TenTelescopes/Skyward200/STL Files (alpha status not oriented)/D200 Astrograph Scope STLs/200mm Astrograph Dovetail.stl

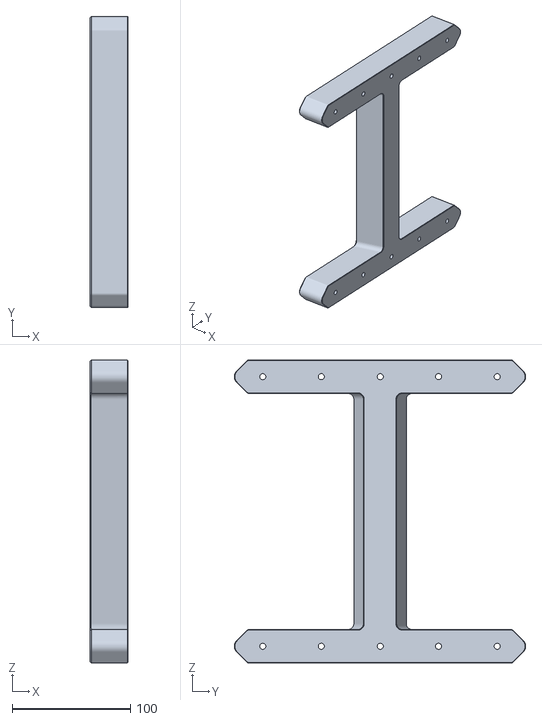
[picture p15: CAD file, 2026-08-10]
STL Files (alpha status not oriented)/D200 Astrograph Scope STLs/200mm Astrograph Dovetail.stl
32.0 x 246.8 x 256.6
