TenTelescopes/Skyward200/STL Files (alpha status not oriented)/D200 Visual Scope STLs/Accessories Printed Parts/Solar Finder Part 2.stl

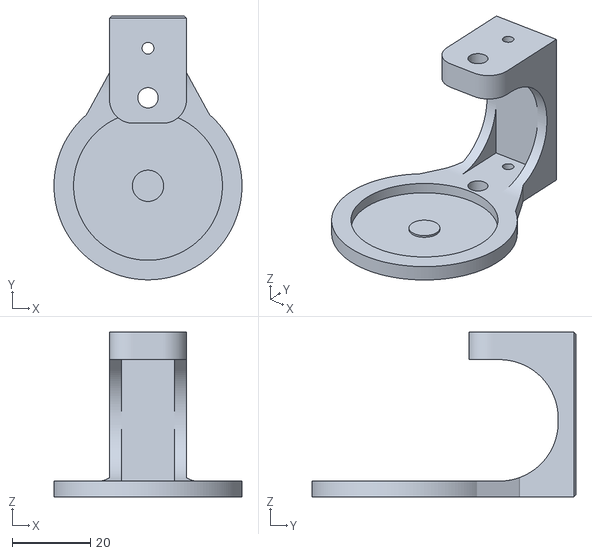
[picture p16: CAD file, 2026-08-24]
STL Files (alpha status not oriented)/D200 Visual Scope STLs/Accessories Printed Parts/Solar Finder Part 2.stl
48.0 x 67.3 x 42.0
