TenTelescopes/Skyward200/STL Files (alpha status not oriented)/D200 Visual Scope STLs/OTA Printed Parts/200mm Mirror Cell Cap.stl

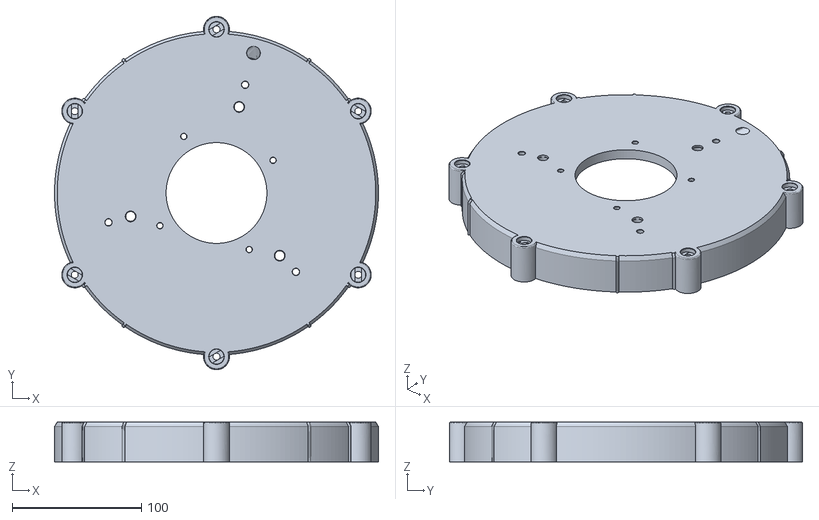
[picture p17: CAD file, 2026-05-24]
STL Files (alpha status not oriented)/D200 Visual Scope STLs/OTA Printed Parts/200mm Mirror Cell Cap.stl
250.8 x 273.5 x 30.9
