TenTelescopes/Skyward200/STL Files (alpha status not oriented)/D200 Visual Scope STLs/Visual Tripod-Mount Printed Parts/200mm Tripod Apex w Docks.stl

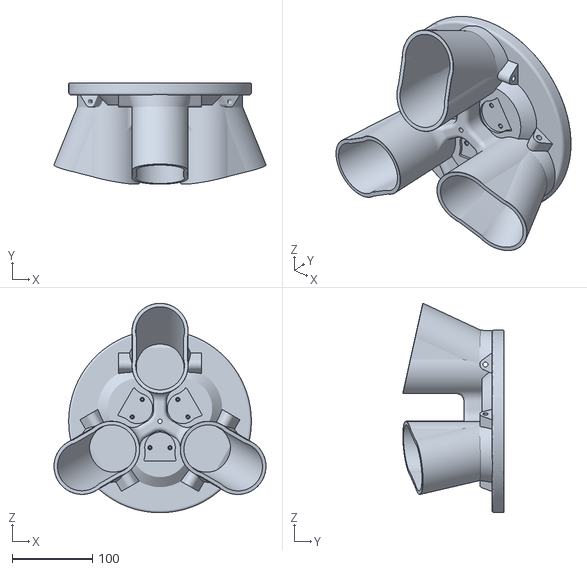
[picture p18: CAD file, 2026-08-18]
STL Files (alpha status not oriented)/D200 Visual Scope STLs/Visual Tripod-Mount Printed Parts/200mm Tripod Apex w Docks.stl
264.4 x 126.5 x 261.1
