TenTelescopes/Skyward200/STL Files (alpha status not oriented)/D200 Visual Scope STLs/Accessories Printed Parts/Phone Dock Mounted Bracket.stl

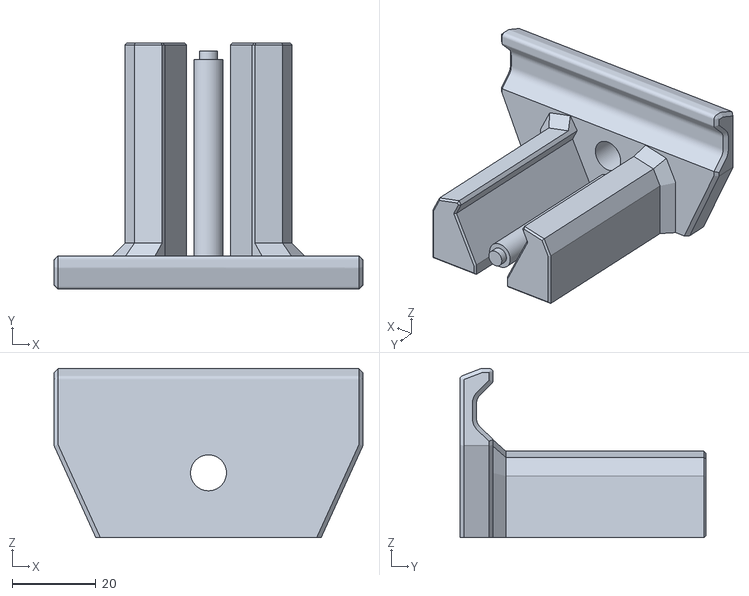
[picture p20: CAD file, 2026-07-30]
STL Files (alpha status not oriented)/D200 Visual Scope STLs/Accessories Printed Parts/Phone Dock Mounted Bracket.stl
74.0 x 59.0 x 40.5
