TenTelescopes/Skyward200/STL Files (alpha status not oriented)/D200 Visual Scope STLs/OTA Printed Parts/200mm Upper Baffle.stl

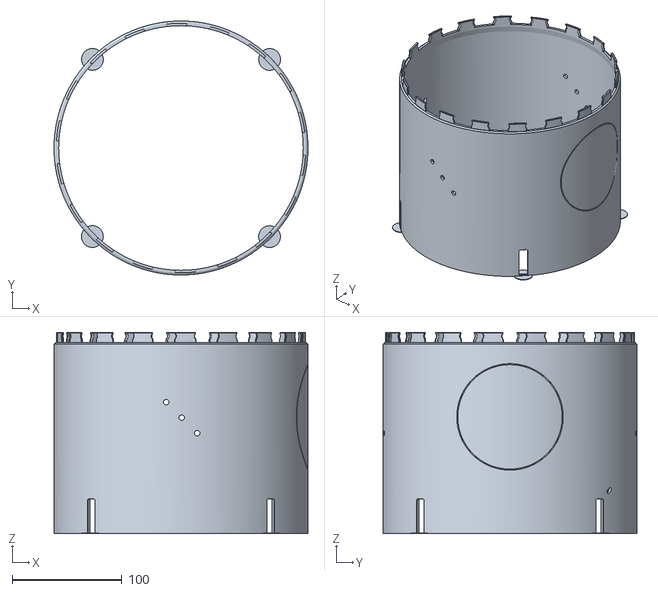
[picture p21: CAD file, 2026-05-24]
STL Files (alpha status not oriented)/D200 Visual Scope STLs/OTA Printed Parts/200mm Upper Baffle.stl
231.9 x 231.9 x 183.6
