TenTelescopes/Skyward200/STL Files (alpha status not oriented)/D200 Visual Scope STLs/Visual Tripod-Mount Printed Parts/200mm TPU Crossbrace Docks x3.stl

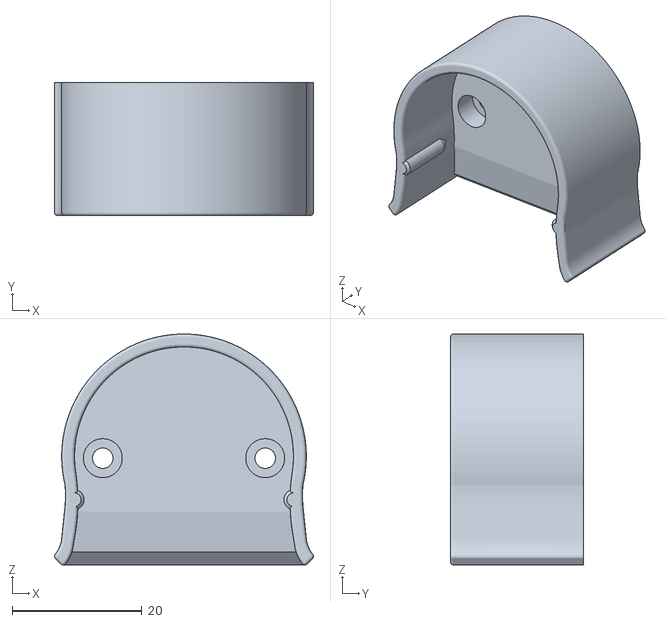
[picture p22: CAD file, 2026-08-18]
STL Files (alpha status not oriented)/D200 Visual Scope STLs/Visual Tripod-Mount Printed Parts/200mm TPU Crossbrace Docks x3.stl
39.9 x 20.5 x 35.6
