TenTelescopes/Skyward200/STL Files (alpha status not oriented)/D200 Astrograph Scope STLs/200mm Astrograph Small Guidescope Computer Mounts.stl

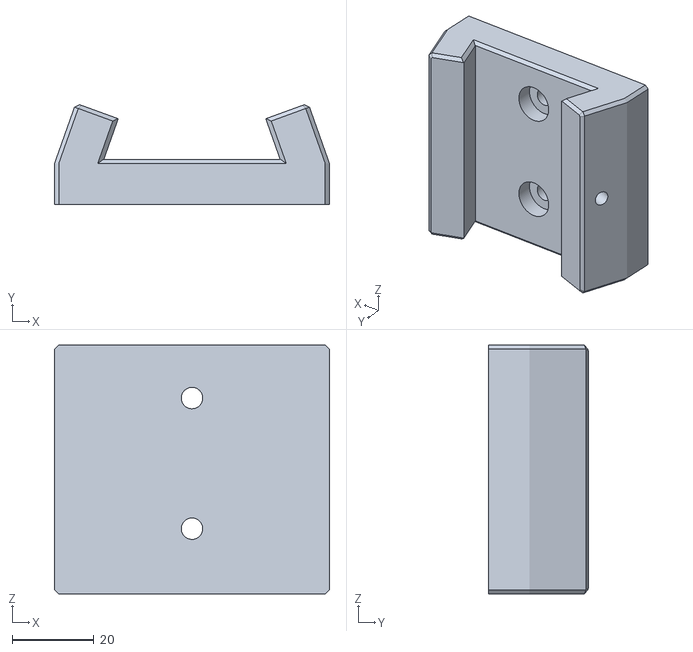
[picture p23: CAD file, 2026-08-10]
STL Files (alpha status not oriented)/D200 Astrograph Scope STLs/200mm Astrograph Small Guidescope Computer Mounts.stl
67.4 x 24.4 x 61.0
