TenTelescopes/Skyward200/STL Files (alpha status not oriented)/D200 Visual Scope STLs/OTA Printed Parts/200mm Slide in Spider.stl

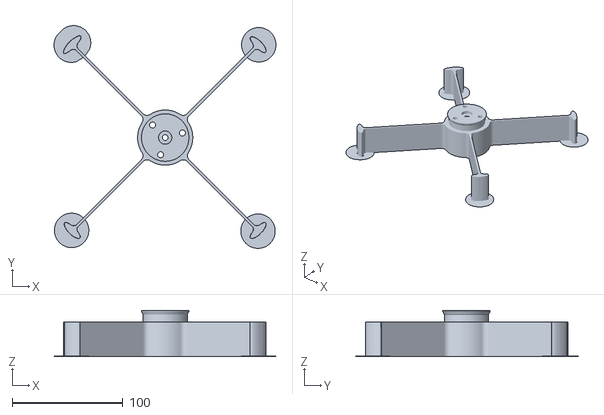
[picture p24: CAD file, 2026-05-23]
STL Files (alpha status not oriented)/D200 Visual Scope STLs/OTA Printed Parts/200mm Slide in Spider.stl
200.5 x 201.2 x 41.6
