TenTelescopes/Skyward200/STL Files (alpha status not oriented)/D200 Visual Scope STLs/Visual Tripod-Mount Printed Parts/200mm Rocker Box Base.stl

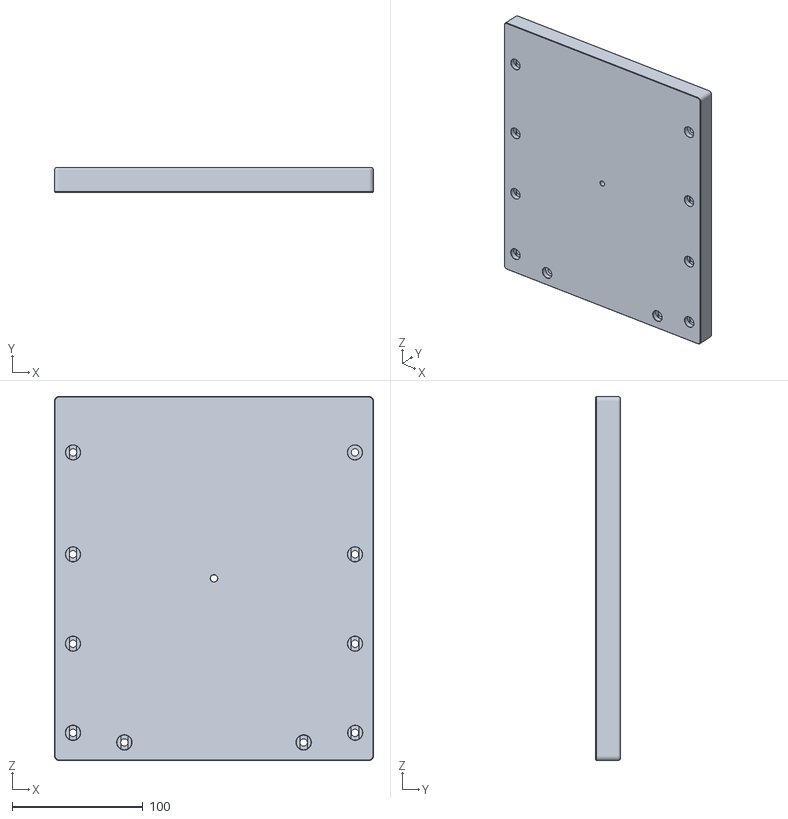
[picture p25: CAD file, 2026-07-23]
STL Files (alpha status not oriented)/D200 Visual Scope STLs/Visual Tripod-Mount Printed Parts/200mm Rocker Box Base.stl
243.6 x 18.8 x 278.0
