TenTelescopes/Skyward200/STL Files (alpha status not oriented)/D200 Astrograph Scope STLs/200mm Astrograph Upper Baffle.stl

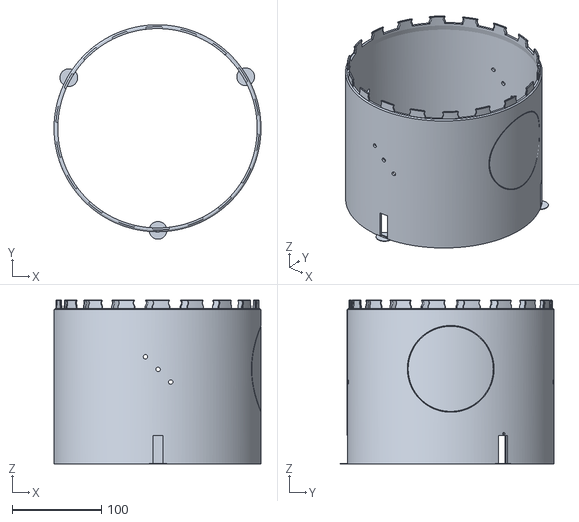
[picture p26: CAD file, 2026-07-06]
STL Files (alpha status not oriented)/D200 Astrograph Scope STLs/200mm Astrograph Upper Baffle.stl
231.9 x 240.3 x 183.6
