TenTelescopes/Skyward200/STL Files (alpha status not oriented)/D200 Visual Scope STLs/Accessories Printed Parts/Phone Dock Threaded Bracket.stl

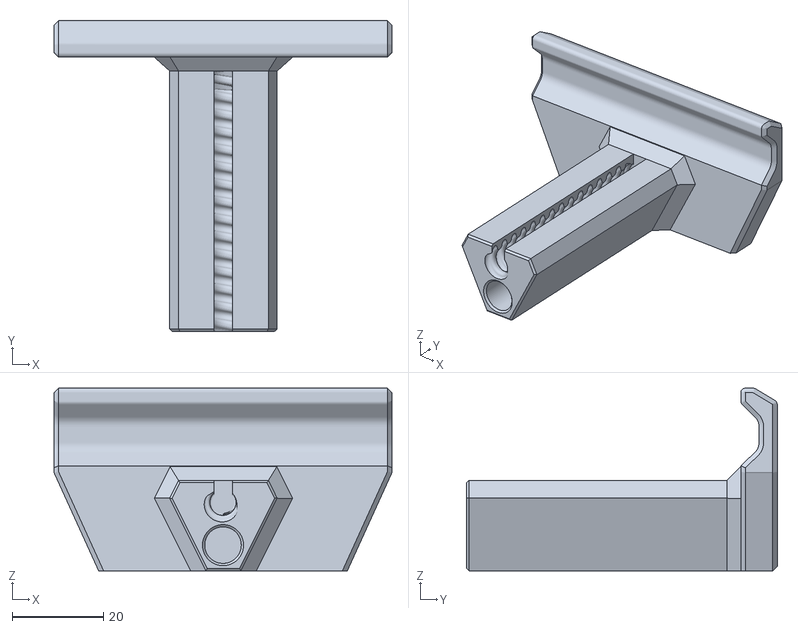
[picture p27: CAD file, 2026-07-21]
STL Files (alpha status not oriented)/D200 Visual Scope STLs/Accessories Printed Parts/Phone Dock Threaded Bracket.stl
74.0 x 68.0 x 40.0
