TenTelescopes/Skyward200/STL Files (alpha status not oriented)/D200 Visual Scope STLs/Visual Tripod-Mount Printed Parts/200mm Tripod Crossbrace Pull Tab x 3.stl

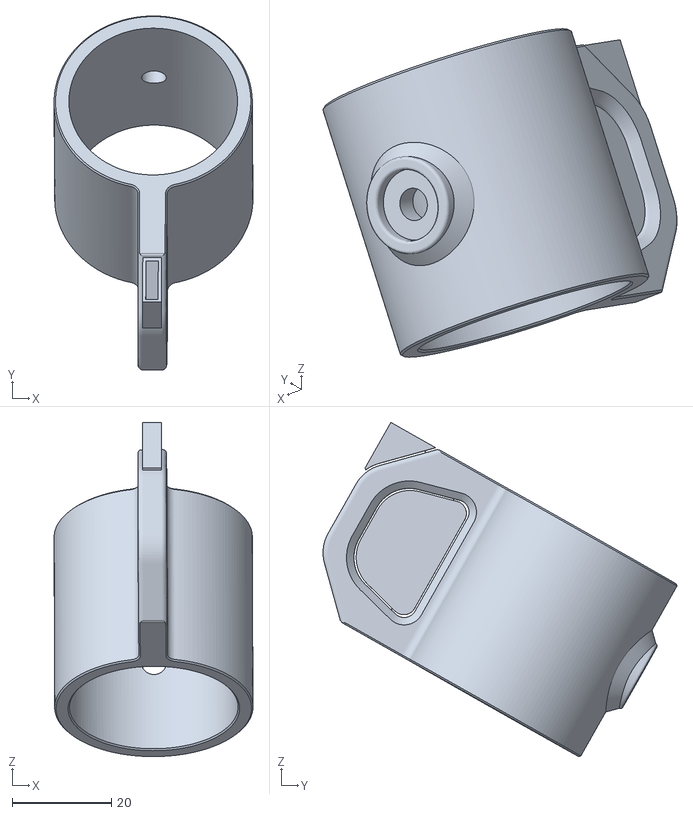
[picture p28: CAD file, 2026-07-21]
STL Files (alpha status not oriented)/D200 Visual Scope STLs/Visual Tripod-Mount Printed Parts/200mm Tripod Crossbrace Pull Tab x 3.stl
40.1 x 71.4 x 67.4
