TenTelescopes/Skyward200/STL Files (alpha status not oriented)/D200 Astrograph Scope STLs/200mm Astrograph Spider Housing.stl

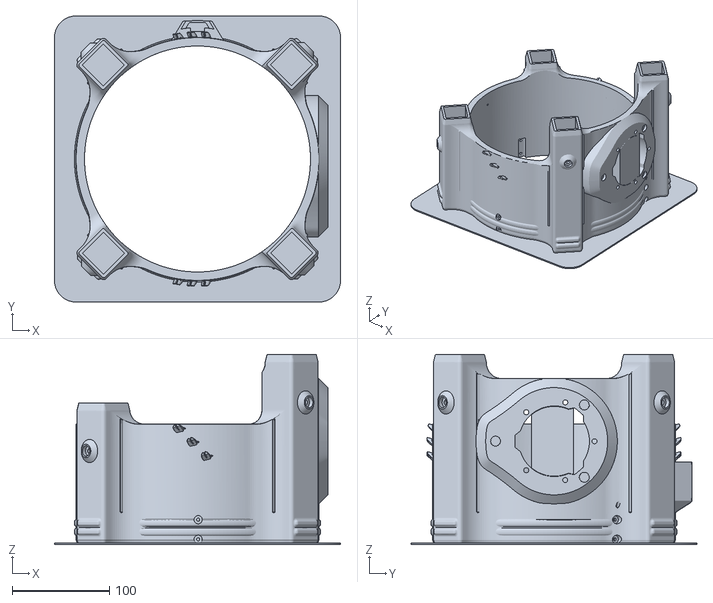
[picture p29: CAD file, 2026-06-09]
STL Files (alpha status not oriented)/D200 Astrograph Scope STLs/200mm Astrograph Spider Housing.stl
294.6 x 294.6 x 196.0
