TenTelescopes/Skyward200/STL Files (alpha status not oriented)/D200 Visual Scope STLs/Accessories Printed Parts/200mm Phone Dock Bridge Mount.stl

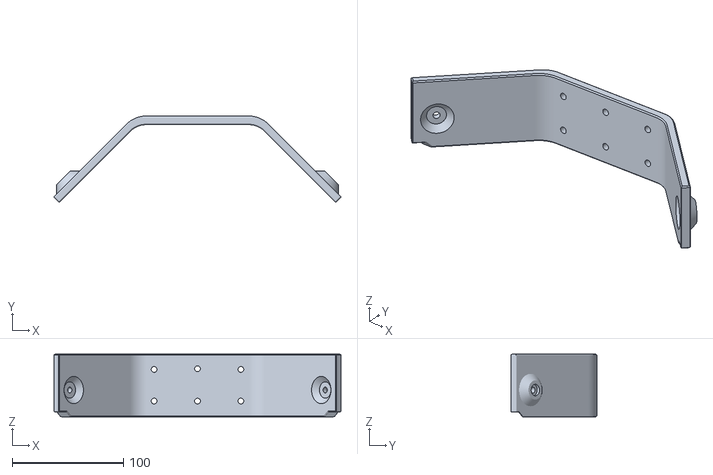
[picture p30: CAD file, 2026-07-06]
STL Files (alpha status not oriented)/D200 Visual Scope STLs/Accessories Printed Parts/200mm Phone Dock Bridge Mount.stl
258.3 x 77.6 x 56.5
