TenTelescopes/Skyward200/STL Files (alpha status not oriented)/D200 Visual Scope STLs/OTA Printed Parts/200mm Mirror Cell.stl

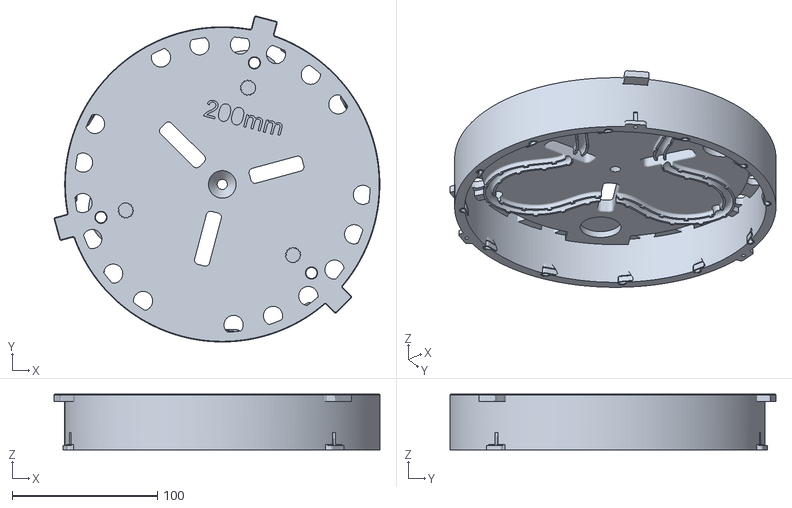
[picture p31: CAD file, 2026-05-14]
STL Files (alpha status not oriented)/D200 Visual Scope STLs/OTA Printed Parts/200mm Mirror Cell.stl
224.5 x 224.6 x 38.5
