TenTelescopes/Skyward200/STL Files (alpha status not oriented)/D200 Visual Scope STLs/Visual Tripod-Mount Printed Parts/200mm Tripod Crossbrace Bracket x 3.stl

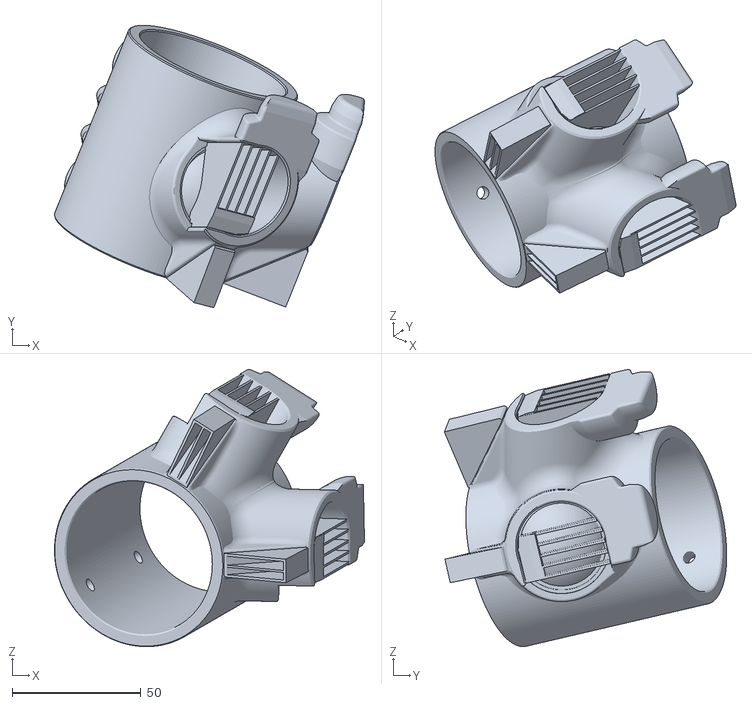
[picture p32: CAD file, 2026-07-21]
STL Files (alpha status not oriented)/D200 Visual Scope STLs/Visual Tripod-Mount Printed Parts/200mm Tripod Crossbrace Bracket x 3.stl
120.5 x 109.8 x 107.8
