TenTelescopes/Skyward200/STL Files (alpha status not oriented)/D200 Astrograph Scope STLs/200mm Astrograph Mirror Cell Rear Cap.stl

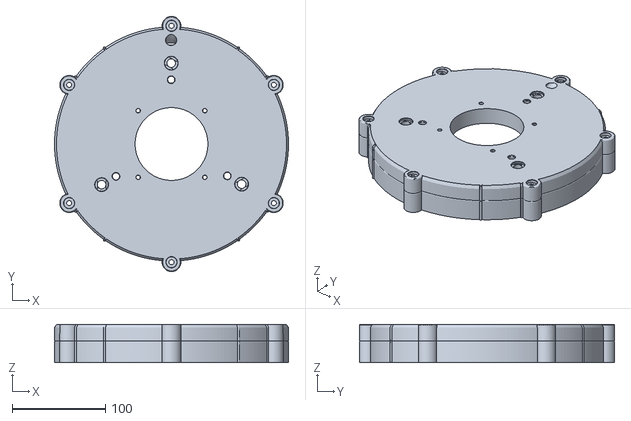
[picture p33: CAD file, 2026-06-09]
STL Files (alpha status not oriented)/D200 Astrograph Scope STLs/200mm Astrograph Mirror Cell Rear Cap.stl
250.8 x 273.5 x 40.9
