TenTelescopes/Skyward200/STL Files (alpha status not oriented)/D200 Visual Scope STLs/Accessories Printed Parts/200mm Solar Filter TPU Gasket.stl

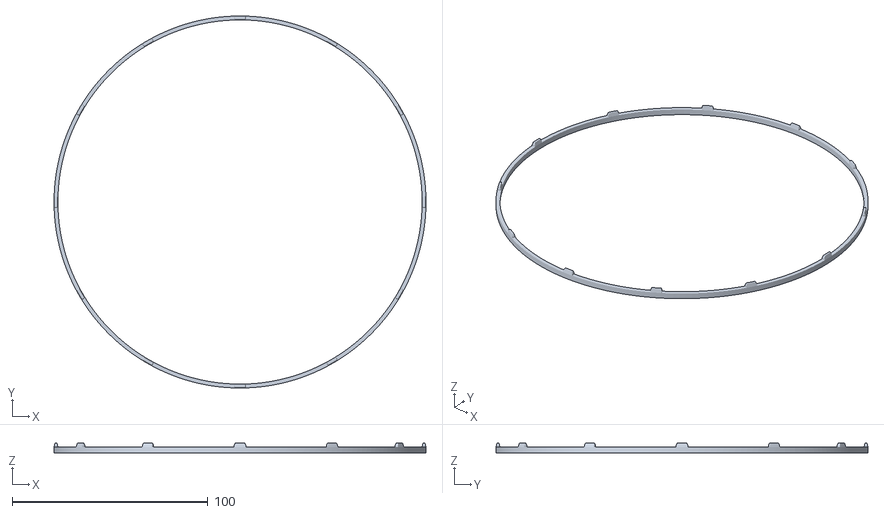
[picture p34: CAD file, 2026-04-28]
STL Files (alpha status not oriented)/D200 Visual Scope STLs/Accessories Printed Parts/200mm Solar Filter TPU Gasket.stl
190.0 x 190.0 x 5.00
