TenTelescopes/Skyward200/STL Files (alpha status not oriented)/D200 Visual Scope STLs/OTA Printed Parts/200mm Mirror Cell Housing w Extra Deadweight.stl

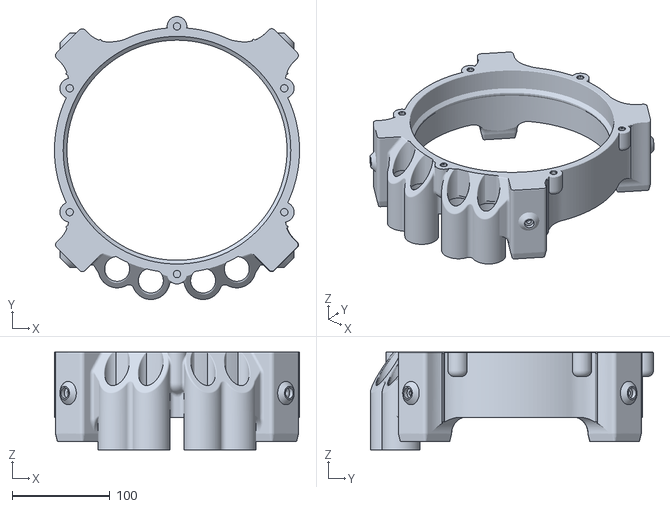
[picture p35: CAD file, 2026-05-01]
STL Files (alpha status not oriented)/D200 Visual Scope STLs/OTA Printed Parts/200mm Mirror Cell Housing w Extra Deadweight.stl
250.6 x 289.4 x 100.1
