TenTelescopes/Skyward200/STL Files (alpha status not oriented)/D200 Visual Scope STLs/Visual Tripod-Mount Printed Parts/200mm Rocker Box Extension Left.stl

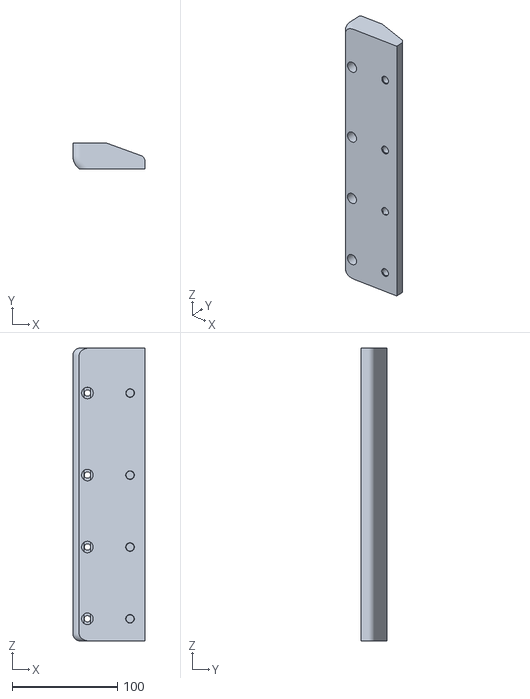
[picture p36: CAD file, 2026-05-24]
STL Files (alpha status not oriented)/D200 Visual Scope STLs/Visual Tripod-Mount Printed Parts/200mm Rocker Box Extension Left.stl
68.5 x 25.0 x 278.0
