TenTelescopes/Skyward200/STL Files (alpha status not oriented)/D200 Astrograph Scope STLs/200mm Astrograph Mirror Cell Housing.stl

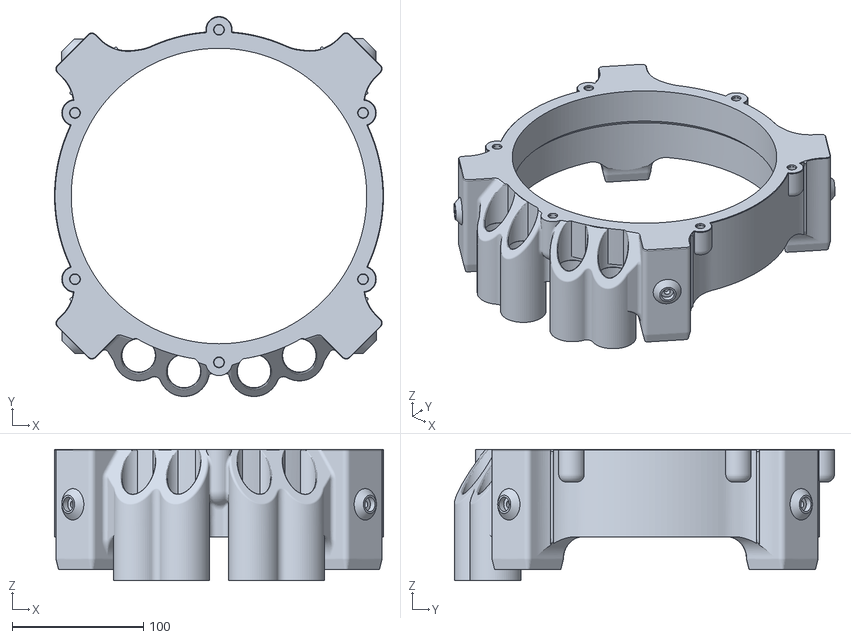
[picture p37: CAD file, 2026-06-08]
STL Files (alpha status not oriented)/D200 Astrograph Scope STLs/200mm Astrograph Mirror Cell Housing.stl
250.6 x 289.4 x 100.1
