TenTelescopes/Skyward200/STL Files (alpha status not oriented)/D200 Visual Scope STLs/Accessories Printed Parts/200mm Solar Filter Retaining Ring.stl

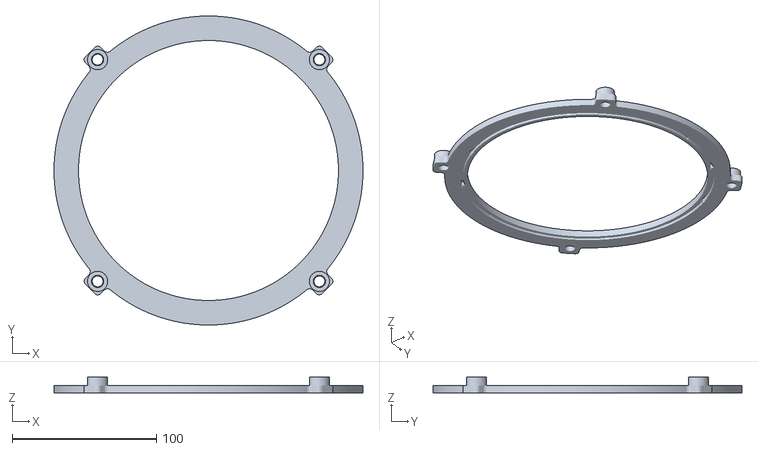
[picture p38: CAD file, 2026-04-28]
STL Files (alpha status not oriented)/D200 Visual Scope STLs/Accessories Printed Parts/200mm Solar Filter Retaining Ring.stl
214.0 x 214.0 x 11.0
