TenTelescopes/Skyward200/STL Files (alpha status not oriented)/D200 Visual Scope STLs/OTA Printed Parts/200mm Mid Truss x 2.stl

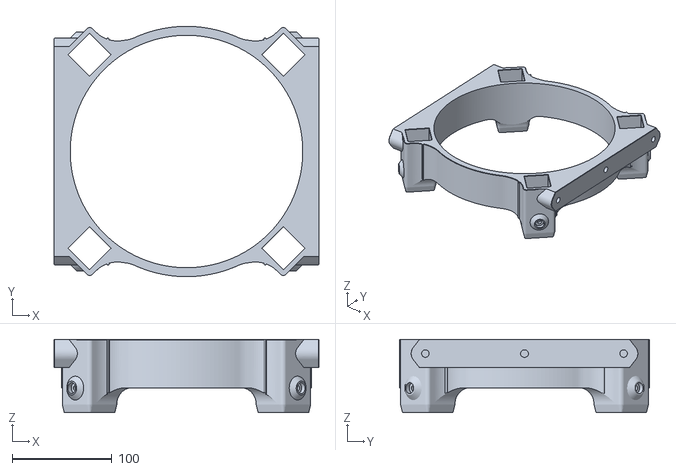
[picture p39: CAD file, 2026-04-20]
STL Files (alpha status not oriented)/D200 Visual Scope STLs/OTA Printed Parts/200mm Mid Truss x 2.stl
265.3 x 250.5 x 73.2
