TenTelescopes/Skyward200/STL Files (alpha status not oriented)/D200 Astrograph Scope STLs/200mm Astrograph 3 Vane Spider.stl

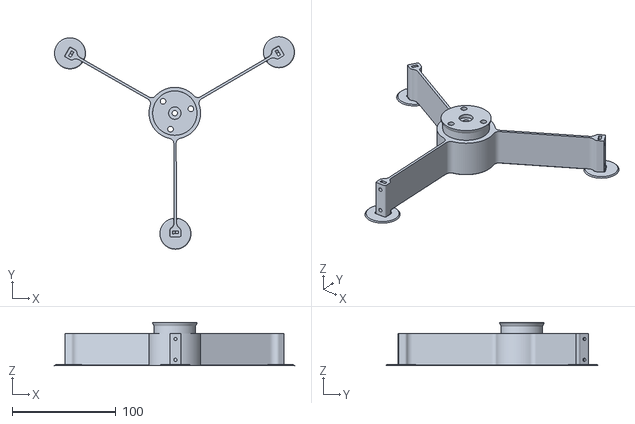
[picture p40: CAD file, 2026-06-08]
STL Files (alpha status not oriented)/D200 Astrograph Scope STLs/200mm Astrograph 3 Vane Spider.stl
231.8 x 205.3 x 41.6
