TenTelescopes/Skyward200/STL Files (alpha status not oriented)/D200 Visual Scope STLs/OTA Printed Parts/200mm Dust Cap Plug x 4.stl

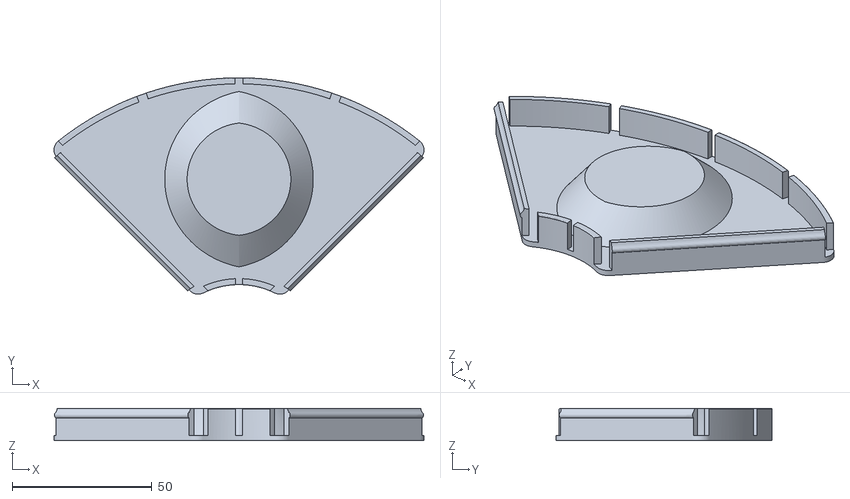
[picture p41: CAD file, 2026-03-12]
STL Files (alpha status not oriented)/D200 Visual Scope STLs/OTA Printed Parts/200mm Dust Cap Plug x 4.stl
132.4 x 77.4 x 11.5
