TenTelescopes/Skyward200/STL Files (alpha status not oriented)/D200 Visual Scope STLs/Visual Tripod-Mount Printed Parts/200mm Alt Bearing Outer Ring x 2.stl

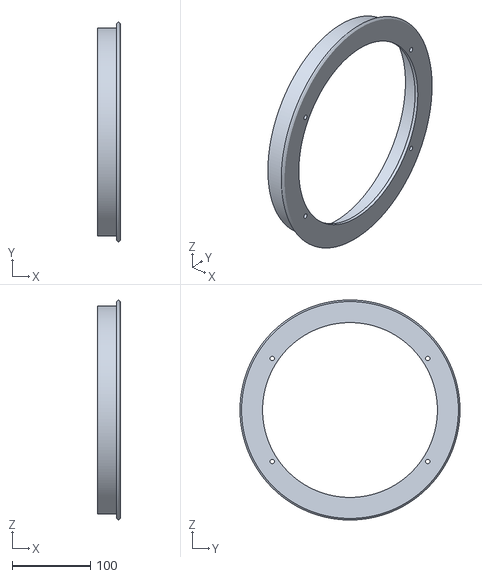
[picture p42: CAD file, 2026-05-14]
STL Files (alpha status not oriented)/D200 Visual Scope STLs/Visual Tripod-Mount Printed Parts/200mm Alt Bearing Outer Ring x 2.stl
29.0 x 280.9 x 280.9
