TenTelescopes/Skyward200/STL Files (alpha status not oriented)/D200 Astrograph Scope STLs/200mm Astrograph Mid Truss x 2.stl

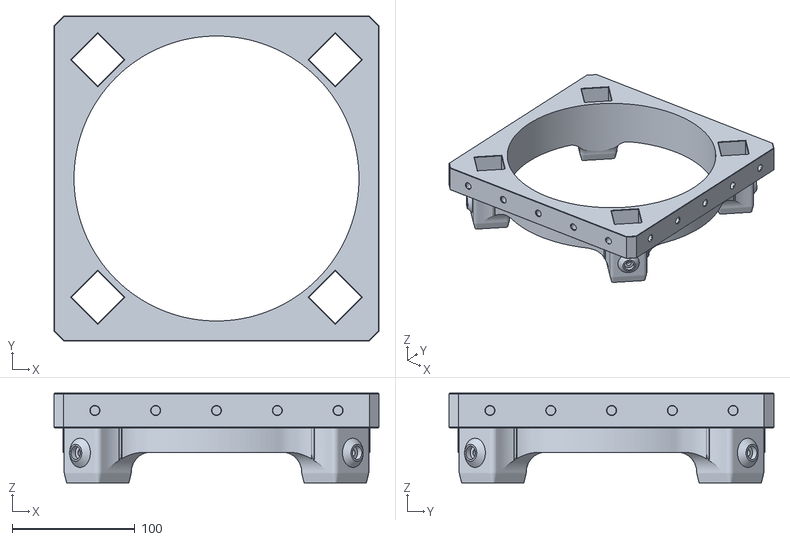
[picture p43: CAD file, 2026-06-08]
STL Files (alpha status not oriented)/D200 Astrograph Scope STLs/200mm Astrograph Mid Truss x 2.stl
265.3 x 265.3 x 73.2
