TenTelescopes/Skyward200/STL Files (alpha status not oriented)/D200 Visual Scope STLs/OTA Printed Parts/200mm Mirror Retaining Ring.stl

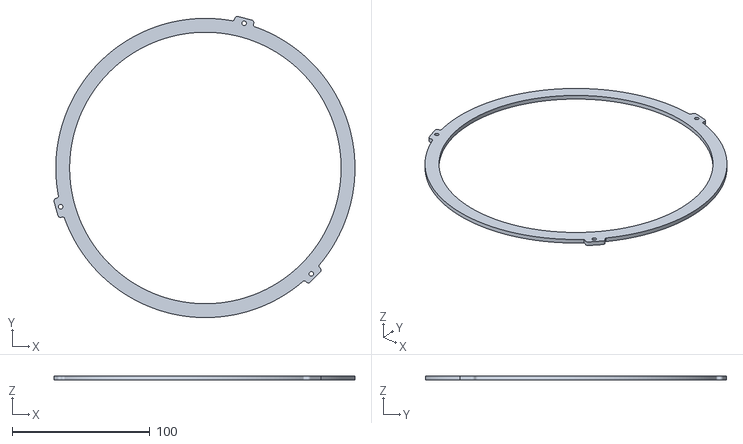
[picture p44: CAD file, 2026-03-12]
STL Files (alpha status not oriented)/D200 Visual Scope STLs/OTA Printed Parts/200mm Mirror Retaining Ring.stl
218.5 x 218.6 x 3.00
