TenTelescopes/Skyward200/STL Files (alpha status not oriented)/D200 Visual Scope STLs/Visual Tripod-Mount Printed Parts/200mm Rocker Box Cross Brace.stl

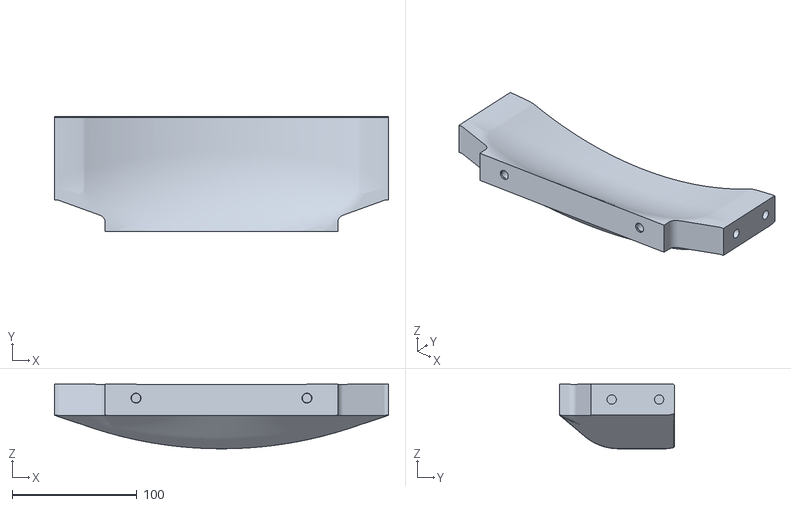
[picture p45: CAD file, 2026-03-12]
STL Files (alpha status not oriented)/D200 Visual Scope STLs/Visual Tripod-Mount Printed Parts/200mm Rocker Box Cross Brace.stl
267.5 x 91.8 x 51.7
