TenTelescopes/Skyward200/STL Files (alpha status not oriented)/D200 Astrograph Scope STLs/200mm Astrograph Tri Bhatinov Dust Cap Plug x3.stl

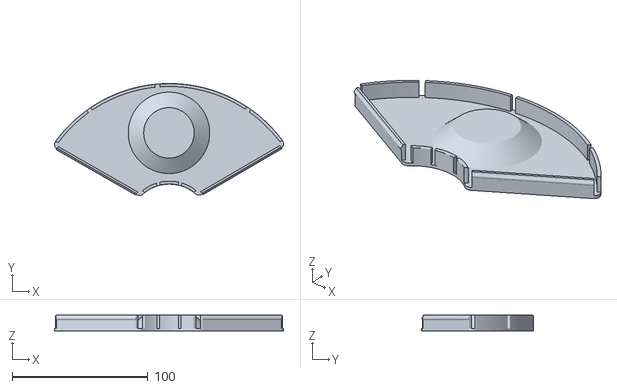
[picture p46: CAD file, 2026-06-08]
STL Files (alpha status not oriented)/D200 Astrograph Scope STLs/200mm Astrograph Tri Bhatinov Dust Cap Plug x3.stl
168.5 x 82.3 x 11.5
