TenTelescopes/Skyward200/STL Files (alpha status not oriented)/D200 Visual Scope STLs/OTA Printed Parts/200mm Spider Rotation Collar.stl

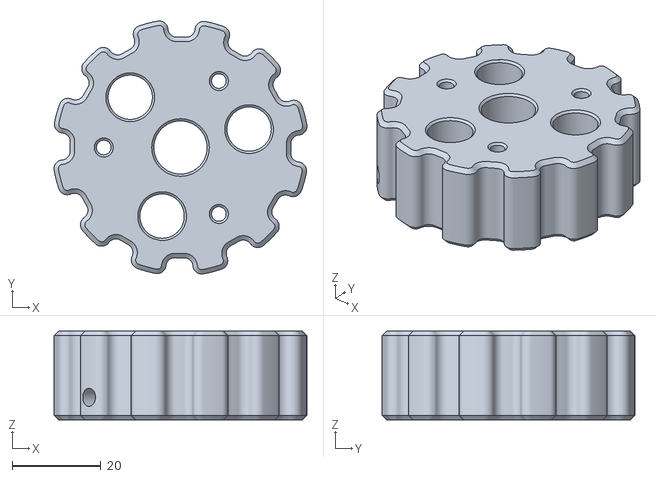
[picture p47: CAD file, 2025-09-29]
STL Files (alpha status not oriented)/D200 Visual Scope STLs/OTA Printed Parts/200mm Spider Rotation Collar.stl
57.1 x 57.1 x 20.0
