TenTelescopes/Skyward200/STL Files (alpha status not oriented)/D200 Visual Scope STLs/Visual Tripod-Mount Printed Parts/200mm Dead Weight Dock.stl

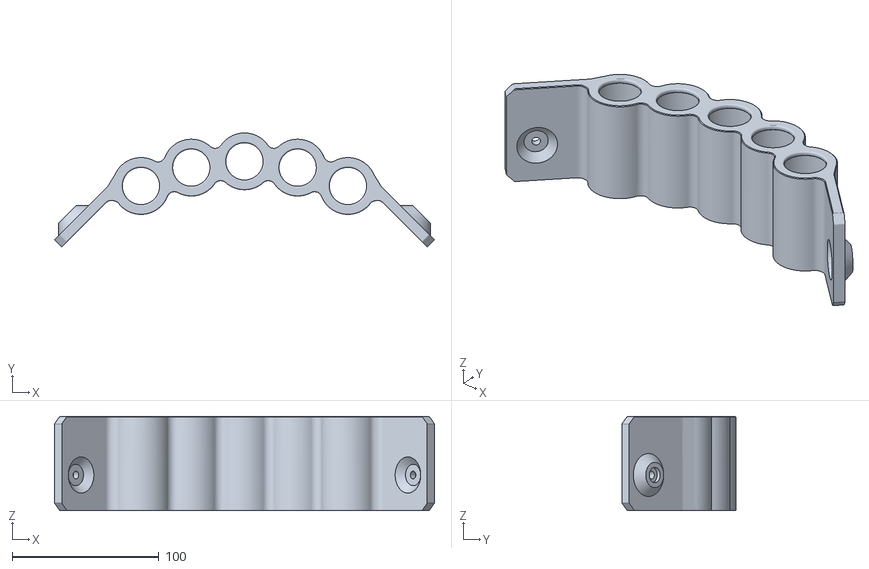
[picture p48: CAD file, 2026-03-12]
STL Files (alpha status not oriented)/D200 Visual Scope STLs/Visual Tripod-Mount Printed Parts/200mm Dead Weight Dock.stl
259.0 x 77.7 x 64.1
