TenTelescopes/Skyward200/STL Files (alpha status not oriented)/D200 Astrograph Scope STLs/200mm Astrograph CrossStruts.stl

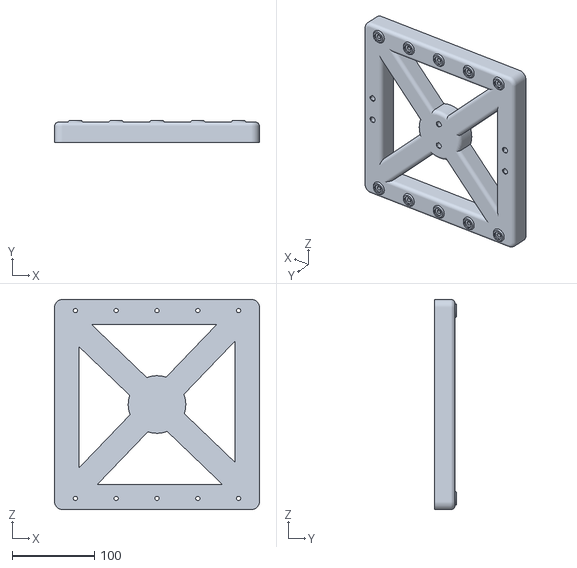
[picture p49: CAD file, 2026-06-08]
STL Files (alpha status not oriented)/D200 Astrograph Scope STLs/200mm Astrograph CrossStruts.stl
249.3 x 27.0 x 255.6
