TenTelescopes/Skyward200/STL Files (alpha status not oriented)/D200 Visual Scope STLs/OTA Printed Parts/200mm 80mm Fan Cover.stl

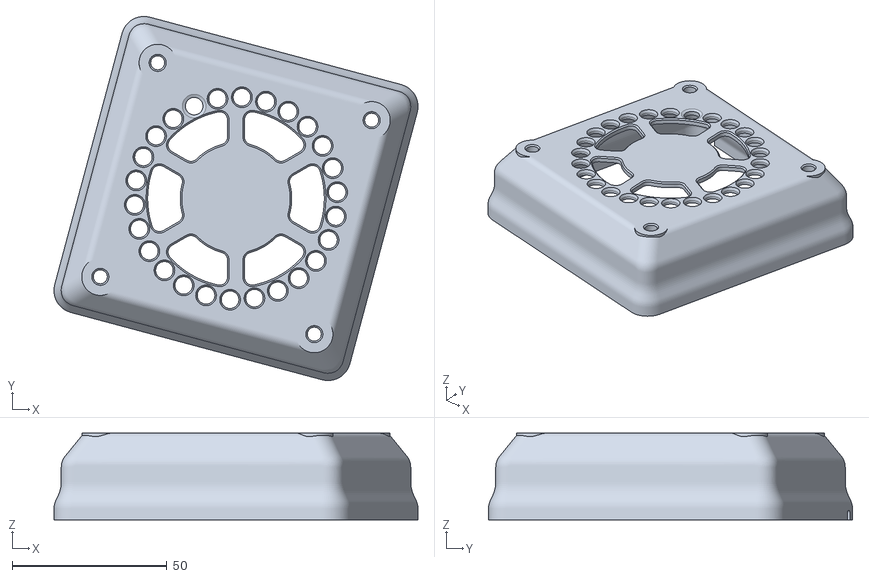
[picture p50: CAD file, 2025-08-20]
STL Files (alpha status not oriented)/D200 Visual Scope STLs/OTA Printed Parts/200mm 80mm Fan Cover.stl
117.5 x 117.5 x 28.0
