TenTelescopes/Skyward200/STL Files (alpha status not oriented)/D200 Visual Scope STLs/Visual Tripod-Mount Printed Parts/200mm Truss Rockerbox Upright Right.stl

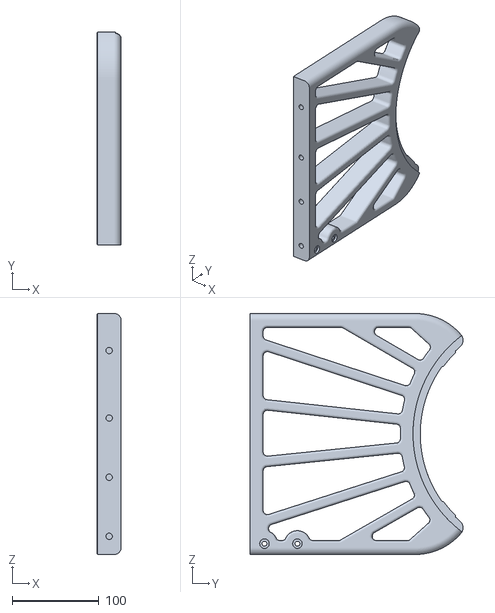
[picture p51: CAD file, 2025-08-16]
STL Files (alpha status not oriented)/D200 Visual Scope STLs/Visual Tripod-Mount Printed Parts/200mm Truss Rockerbox Upright Right.stl
28.0 x 245.9 x 278.0
