TenTelescopes/Skyward200/STL Files (alpha status not oriented)/D200 Astrograph Scope STLs/D203 Smooth Astrograph Baffle v2 x2.stl

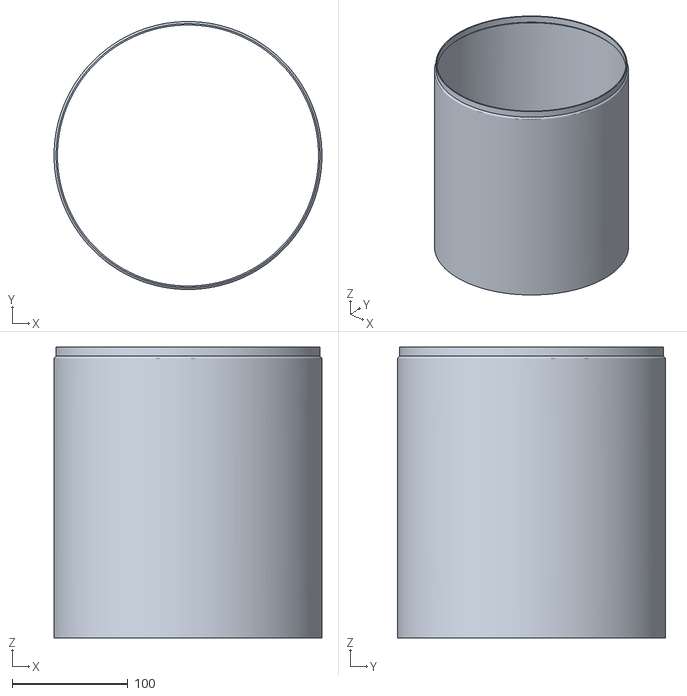
[picture p52: CAD file, 2026-04-28]
STL Files (alpha status not oriented)/D200 Astrograph Scope STLs/D203 Smooth Astrograph Baffle v2 x2.stl
231.8 x 231.8 x 251.8
