TenTelescopes/Skyward200/STL Files (alpha status not oriented)/D200 Visual Scope STLs/OTA Printed Parts/200mm Mirror Cell TPU Shear Puck.stl

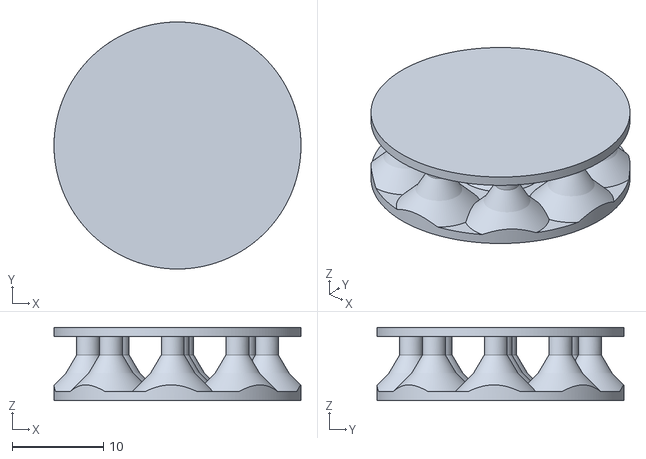
[picture p53: CAD file, 2025-08-16]
STL Files (alpha status not oriented)/D200 Visual Scope STLs/OTA Printed Parts/200mm Mirror Cell TPU Shear Puck.stl
27.0 x 27.0 x 8.00
