TenTelescopes/Skyward200/STL Files (alpha status not oriented)/D200 Astrograph Scope STLs/Dew Fan Contoller Mount.stl

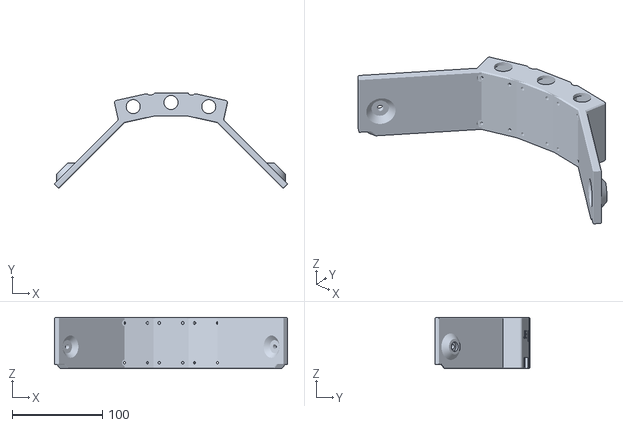
[picture p54: CAD file, 2026-03-12]
STL Files (alpha status not oriented)/D200 Astrograph Scope STLs/Dew Fan Contoller Mount.stl
258.3 x 105.8 x 56.5
