TenTelescopes/Skyward200/STL Files (alpha status not oriented)/D200 Visual Scope STLs/OTA Printed Parts/200mm Secondary Ball.stl

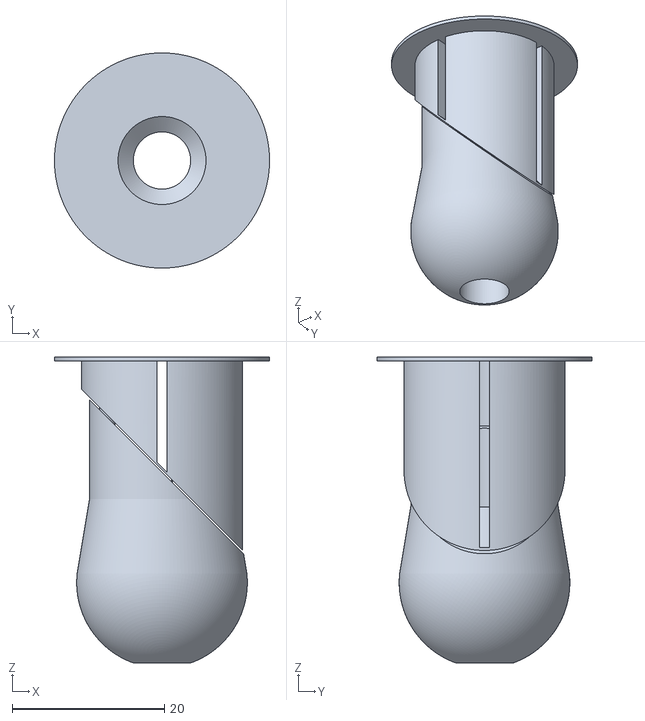
[picture p55: CAD file, 2025-08-11]
STL Files (alpha status not oriented)/D200 Visual Scope STLs/OTA Printed Parts/200mm Secondary Ball.stl
28.2 x 28.2 x 40.1
