TenTelescopes/Skyward200/STL Files (alpha status not oriented)/D200 Visual Scope STLs/Visual Tripod-Mount Printed Parts/200mm Tripod Foot x3.stl

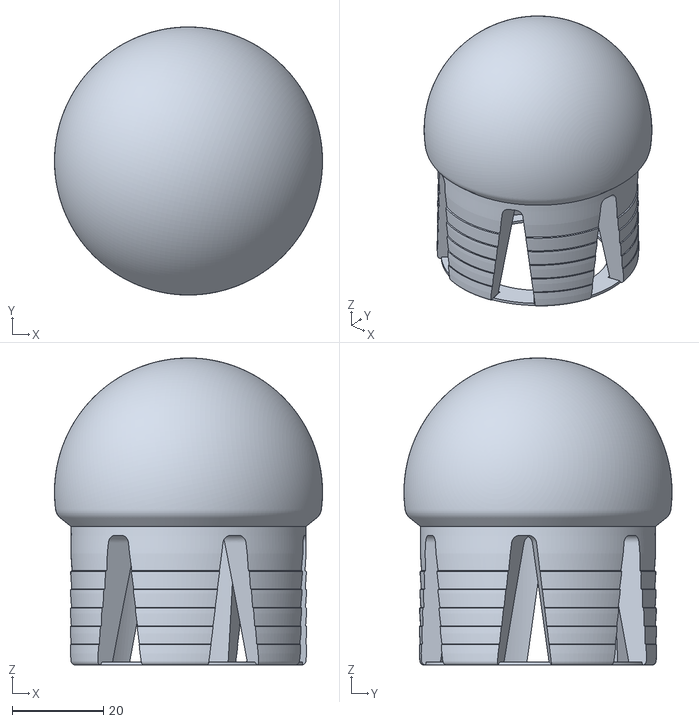
[picture p56: CAD file, 2025-08-16]
STL Files (alpha status not oriented)/D200 Visual Scope STLs/Visual Tripod-Mount Printed Parts/200mm Tripod Foot x3.stl
58.7 x 58.7 x 67.2
