TenTelescopes/Skyward200/STL Files (alpha status not oriented)/D200 Astrograph Scope STLs/Dew Controller Back Cover x 3.stl

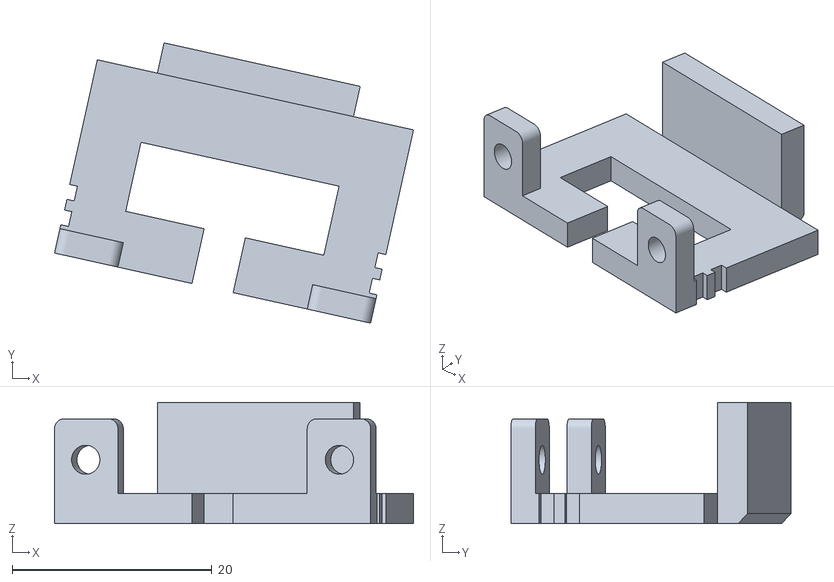
[picture p57: CAD file, 2026-03-12]
STL Files (alpha status not oriented)/D200 Astrograph Scope STLs/Dew Controller Back Cover x 3.stl
35.9 x 28.0 x 12.1
