TenTelescopes/Skyward200/STL Files (alpha status not oriented)/D200 Astrograph Scope STLs/Mele Mini PC Mount.stl

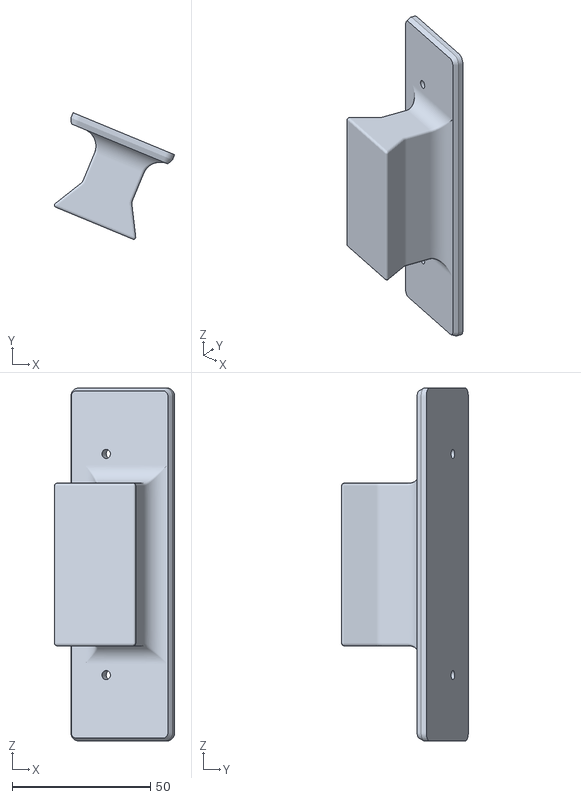
[picture p58: CAD file, 2025-06-24]
STL Files (alpha status not oriented)/D200 Astrograph Scope STLs/Mele Mini PC Mount.stl
43.5 x 45.8 x 127.7
